festlv/oralix-ac65s-controller/oralix-ac-controller/zcd-sim.asc

D1: diode; MUR460
D2: diode; MUR460
R1: res; 47K
R2: res; 47K
R3: res; 10k
R4: res; 10k
R5: res; 1000000
U1: 4N25
U2: 4N25
V1: voltage; SINE(0 230 50)
V2: voltage; 12
Named nets: 0
.tran 1 uic
